vakym4273-max/Wall-mounted-organizers-tweezers-files-drills-/Media/Photos/IMG20251119152010.jpg

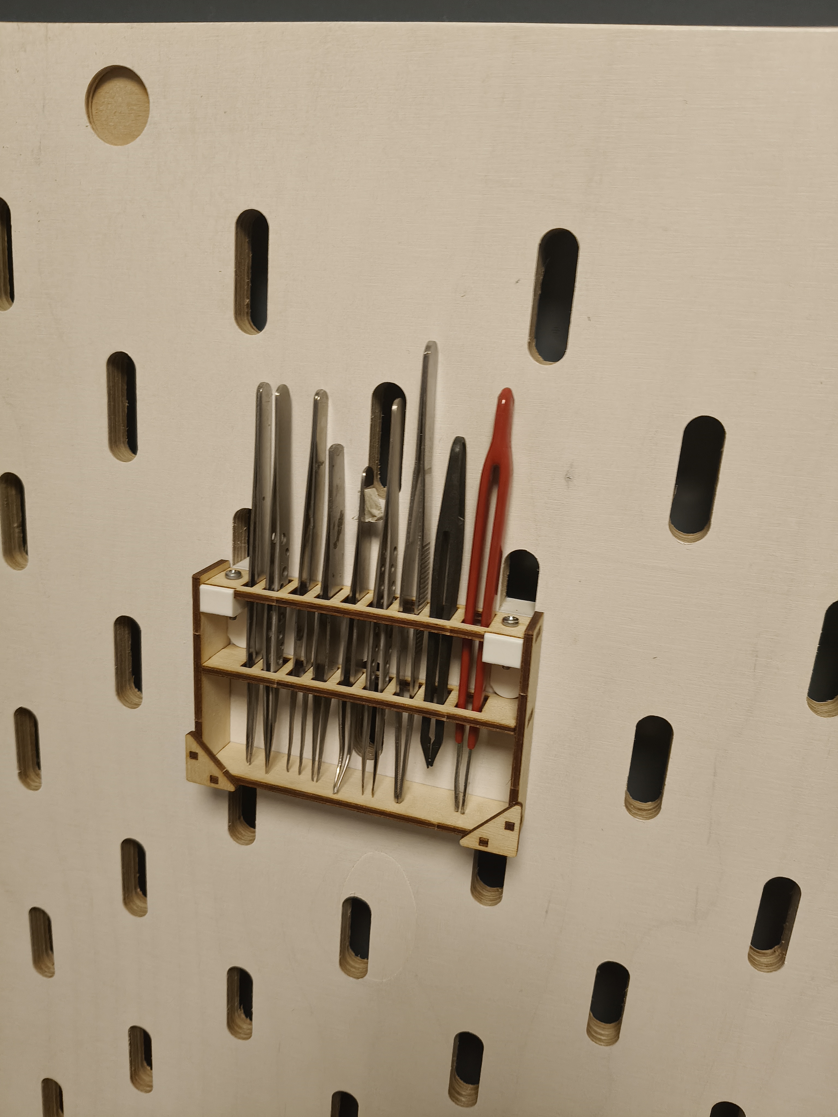
Media/Photos/IMG20251119152010.jpg
