vakym4273-max/Wall-mounted-organizers-tweezers-files-drills-/Media/Photos/IMG20251119174919.jpg

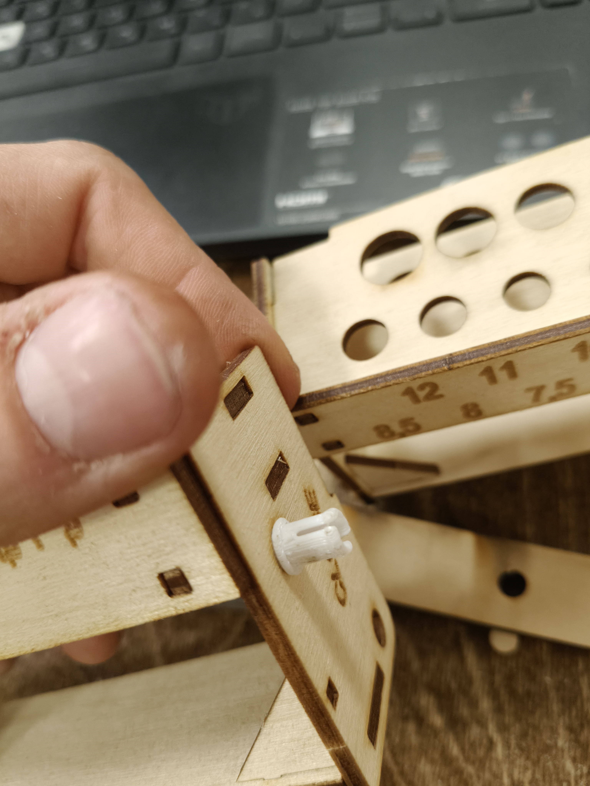
Media/Photos/IMG20251119174919.jpg
