vakym4273-max/Wall-mounted-organizers-tweezers-files-drills-/Media/Photos/IMG20251120174520.jpg

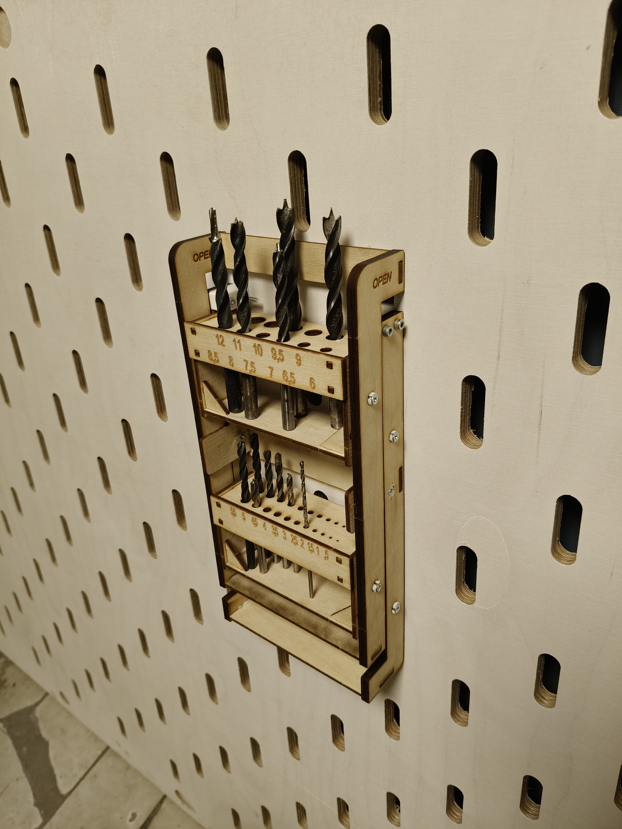
Media/Photos/IMG20251120174520.jpg
