vakym4273-max/Wall-mounted-organizers-tweezers-files-drills-/CAD/SolidWorks/Надфили органайзер/5 Полка средняя надфили.SLDPRT

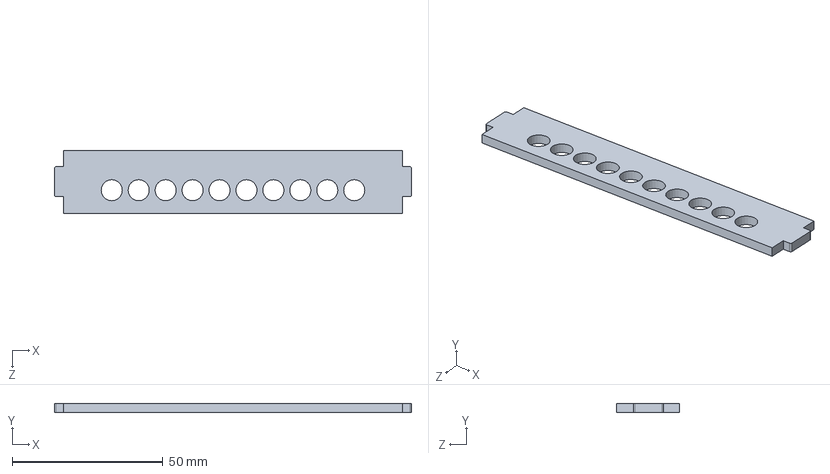
[picture p20: CAD file, 2025-11-26]
CAD/SolidWorks/Надфили органайзер/5 Полка средняя надфили.SLDPRT
118.5 x 3.00 x 20.8 mm
