vakym4273-max/Wall-mounted-organizers-tweezers-files-drills-/CAD/SolidWorks/Пинцеты органайзер/5 Полка средняя пинцеты.SLDPRT

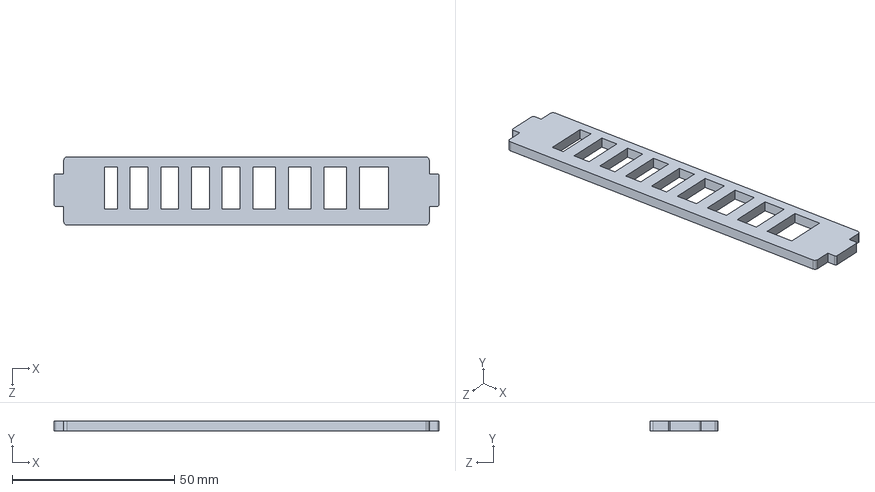
[picture p21: CAD file, 2025-11-26]
CAD/SolidWorks/Пинцеты органайзер/5 Полка средняя пинцеты.SLDPRT
118.5 x 3.00 x 21.0 mm
