vakym4273-max/Wall-mounted-organizers-tweezers-files-drills-/CAD/SolidWorks/Свёрла органайзер/5 Стенка ячейки.SLDPRT

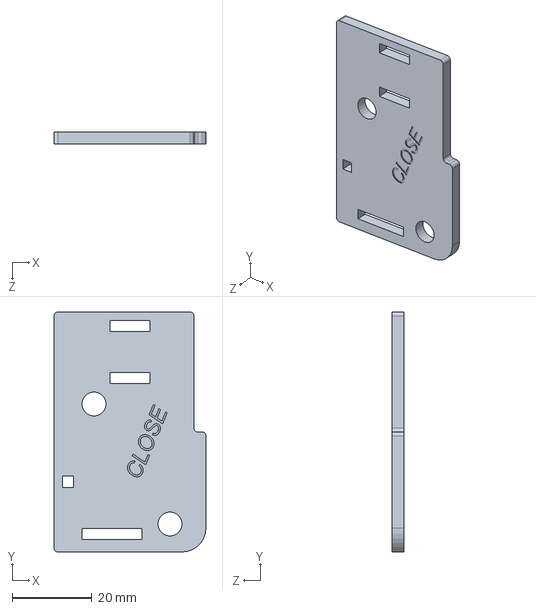
[picture p22: CAD file, 2025-11-26]
CAD/SolidWorks/Свёрла органайзер/5 Стенка ячейки.SLDPRT
38.0 x 60.0 x 3.00 mm
