vakym4273-max/Wall-mounted-organizers-tweezers-files-drills-/CAD/SolidWorks/Свёрла органайзер/3 Стенка основа свёрла.SLDPRT

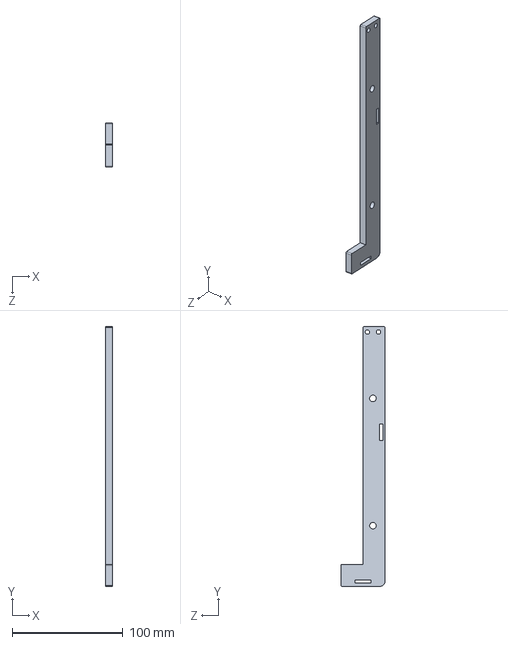
[picture p23: CAD file, 2025-11-26]
CAD/SolidWorks/Свёрла органайзер/3 Стенка основа свёрла.SLDPRT
6.00 x 235.0 x 40.0 mm
