vakym4273-max/Wall-mounted-organizers-tweezers-files-drills-/CAD/SolidWorks/Надфили органайзер/4 Стенка надфиди.SLDPRT

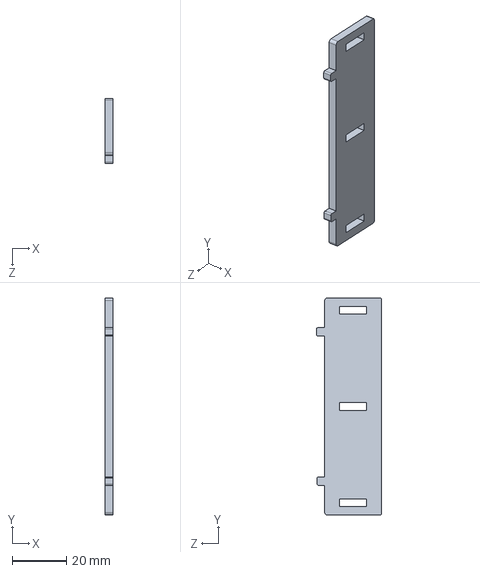
[picture p24: CAD file, 2025-11-26]
CAD/SolidWorks/Надфили органайзер/4 Стенка надфиди.SLDPRT
3.00 x 80.0 x 24.0 mm
