vakym4273-max/Wall-mounted-organizers-tweezers-files-drills-/CAD/SolidWorks/Надфили органайзер/8 Маркировка.SLDPRT

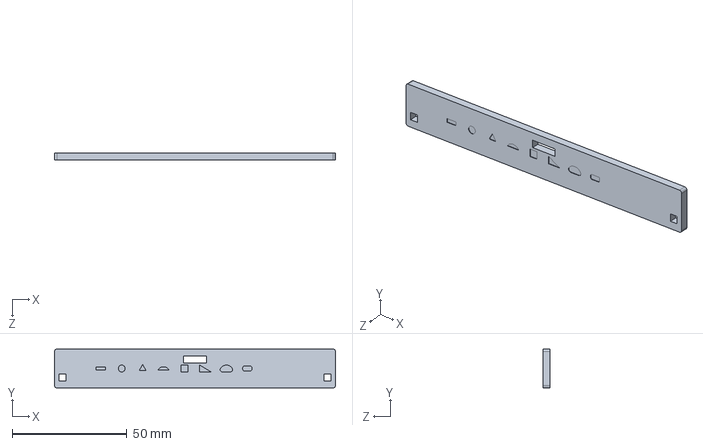
[picture p26: CAD file, 2025-11-26]
CAD/SolidWorks/Надфили органайзер/8 Маркировка.SLDPRT
122.5 x 17.0 x 3.00 mm
