vakym4273-max/Wall-mounted-organizers-tweezers-files-drills-/CAD/SolidWorks/Пинцеты органайзер/3 Полка верхняя Пинцеты.SLDPRT

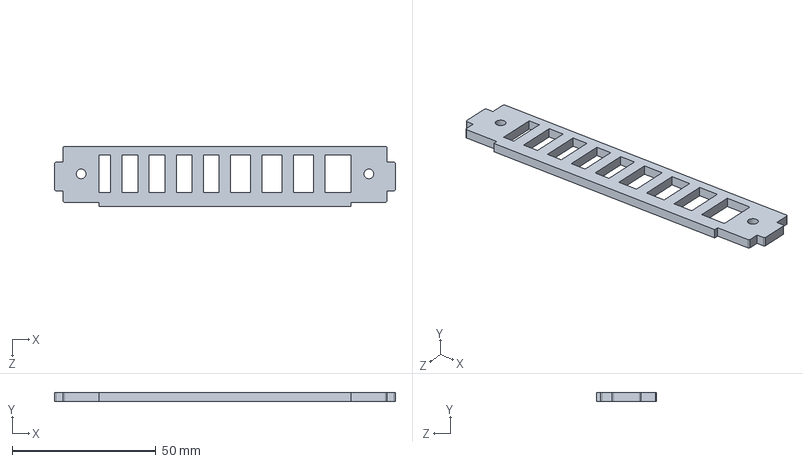
[picture p27: CAD file, 2025-11-26]
CAD/SolidWorks/Пинцеты органайзер/3 Полка верхняя Пинцеты.SLDPRT
118.5 x 3.00 x 21.0 mm
