vakym4273-max/Wall-mounted-organizers-tweezers-files-drills-/CAD/SolidWorks/Свёрла органайзер/10 Уголок свёрла.SLDPRT

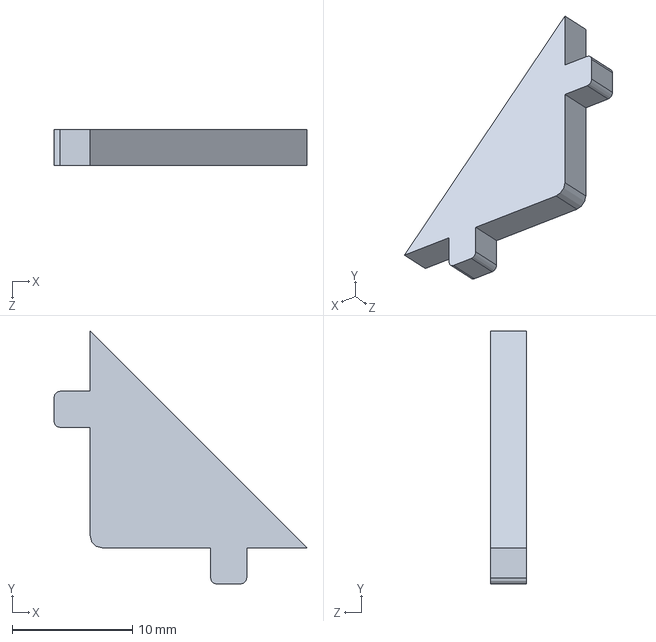
[picture p28: CAD file, 2025-11-26]
CAD/SolidWorks/Свёрла органайзер/10 Уголок свёрла.SLDPRT
21.0 x 21.0 x 3.00 mm
