vakym4273-max/Wall-mounted-organizers-tweezers-files-drills-/CAD/SolidWorks/Надфили органайзер/3 Полка верхняя надфили.SLDPRT

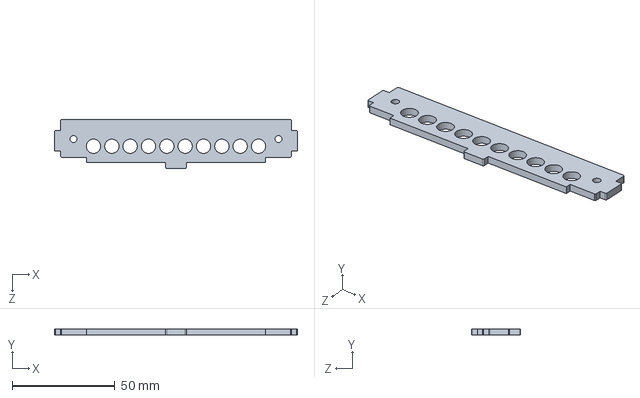
[picture p29: CAD file, 2025-11-26]
CAD/SolidWorks/Надфили органайзер/3 Полка верхняя надфили.SLDPRT
118.5 x 3.00 x 24.0 mm
