vakym4273-max/Wall-mounted-organizers-tweezers-files-drills-/CAD/SolidWorks/Свёрла органайзер/7 Полка ячейки верхняя.SLDPRT

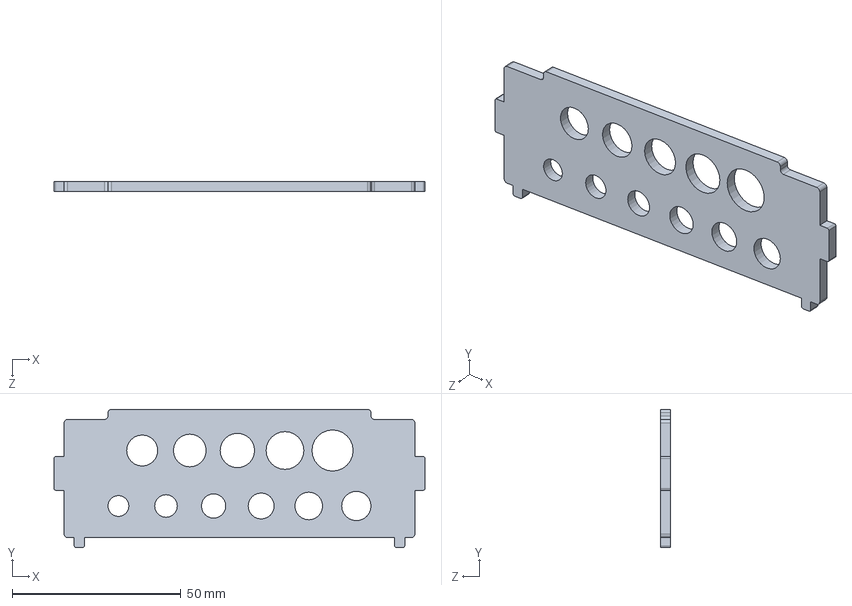
[picture p30: CAD file, 2025-11-26]
CAD/SolidWorks/Свёрла органайзер/7 Полка ячейки верхняя.SLDPRT
110.0 x 41.0 x 3.00 mm
