vakym4273-max/Wall-mounted-organizers-tweezers-files-drills-/CAD/SolidWorks/Свёрла органайзер/8 Полка ячейки средняя.SLDPRT

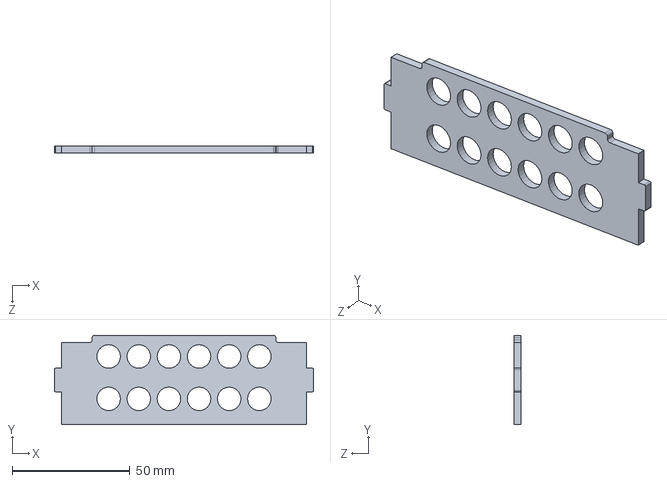
[picture p31: CAD file, 2025-11-26]
CAD/SolidWorks/Свёрла органайзер/8 Полка ячейки средняя.SLDPRT
110.0 x 38.0 x 3.00 mm
