vakym4273-max/Wall-mounted-organizers-tweezers-files-drills-/CAD/SolidWorks/Свёрла органайзер/11 низ.SLDPRT

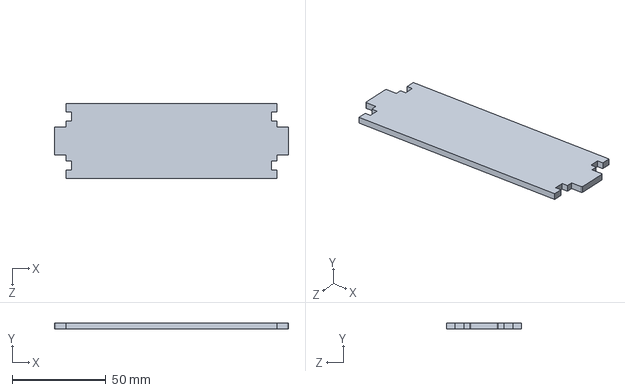
[picture p32: CAD file, 2025-11-26]
CAD/SolidWorks/Свёрла органайзер/11 низ.SLDPRT
124.5 x 3.00 x 40.0 mm
