vakym4273-max/Wall-mounted-organizers-tweezers-files-drills-/CAD/SolidWorks/Свёрла органайзер/6 Полка ячейки нижняя.SLDPRT

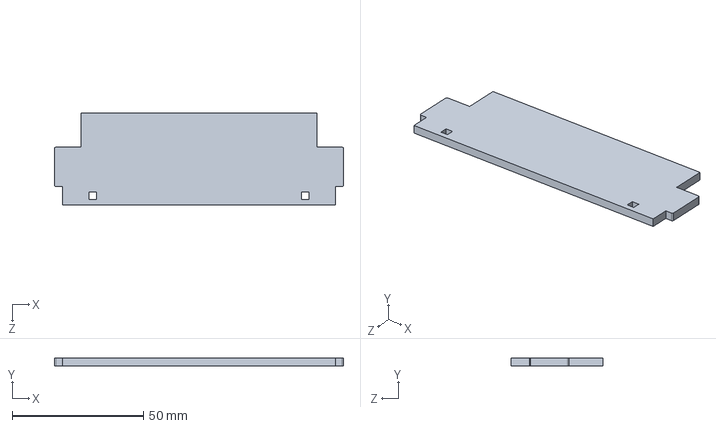
[picture p33: CAD file, 2025-11-26]
CAD/SolidWorks/Свёрла органайзер/6 Полка ячейки нижняя.SLDPRT
110.0 x 3.00 x 35.0 mm
