vakym4273-max/Wall-mounted-organizers-tweezers-files-drills-/CAD/SolidWorks/Свёрла органайзер/13.1 маркировка свёрла верх.SLDPRT

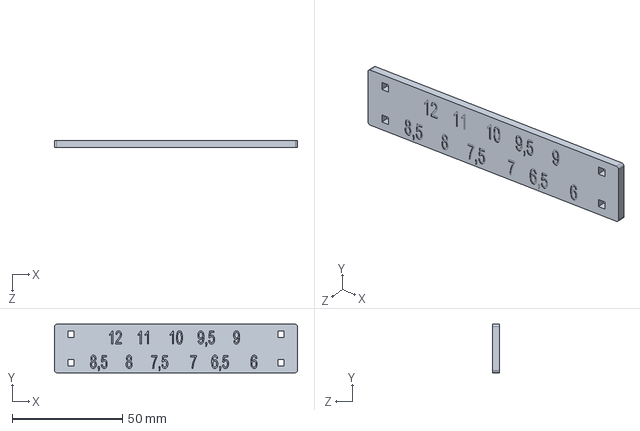
[picture p34: CAD file, 2025-11-26]
CAD/SolidWorks/Свёрла органайзер/13.1 маркировка свёрла верх.SLDPRT
110.0 x 22.0 x 3.00 mm
